gargum/Iyada/kiraibuilds/iyada/keymaps/steno/layers.h

//This file exists for the sake of convenience, specifically in order to make creating user-generated keymaps with a large number of layers less difficult.

#include QMK_KEYBOARD_H

// Keymap Layer Declarations
//
#define _STENO 0
